emeb/H730-Audio/Firmware/common/cyclesleep.h

/*
 * cyclesleep.h - zyp's cycle counter sleep routines
 * 09-05-15 E. Brombaugh - updated for F7 and HAL
 * 03-20-17 E. Brombaugh - fixed wrap bug, update comments
 */

#ifndef __cyclesleep__
#define __cyclesleep__

#include "stm32h7xx_hal.h"

void cyccnt_enable(void);
void cyclesleep(uint32_t cycles);
uint32_t cyclegoal(uint32_t cycles);
uint32_t cyclegoal_ms(uint32_t ms);
uint32_t cyclecheck(uint32_t goal);
void delay(uint32_t ms);
void start_meas(void);
void end_meas(void);
void get_meas(uint32_t *act, uint32_t *tot);

#endif
